sphawes/fiber-laser-pcb-fab/img/xt-inspect-gcode.png

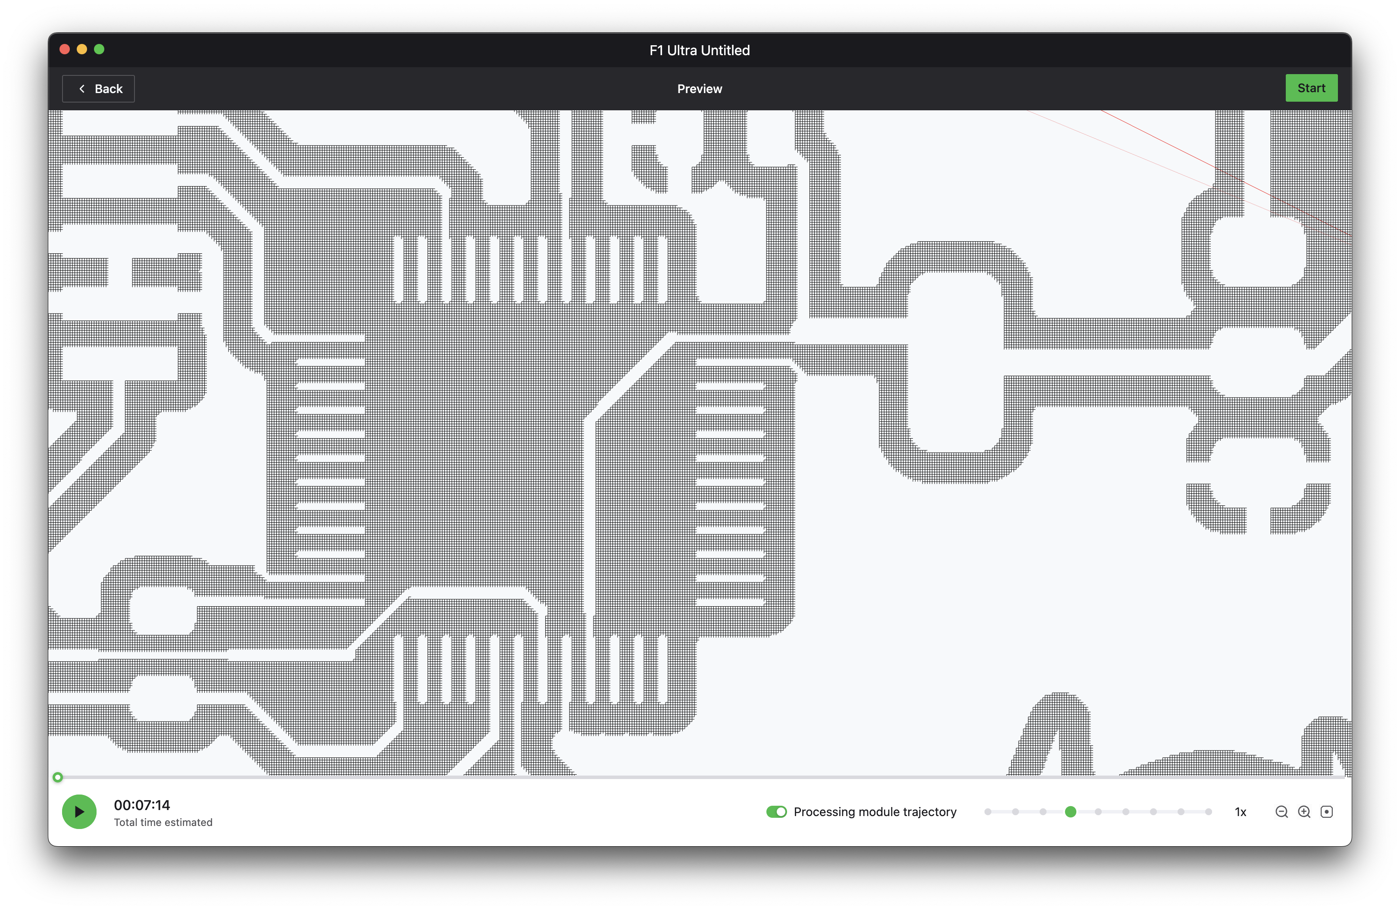
img/xt-inspect-gcode.png
